jujunet37/CAM10-Astronomy-camera/Cam 10 ASCOM version/Component list/Bill_Of_Mats_Cam10R.png

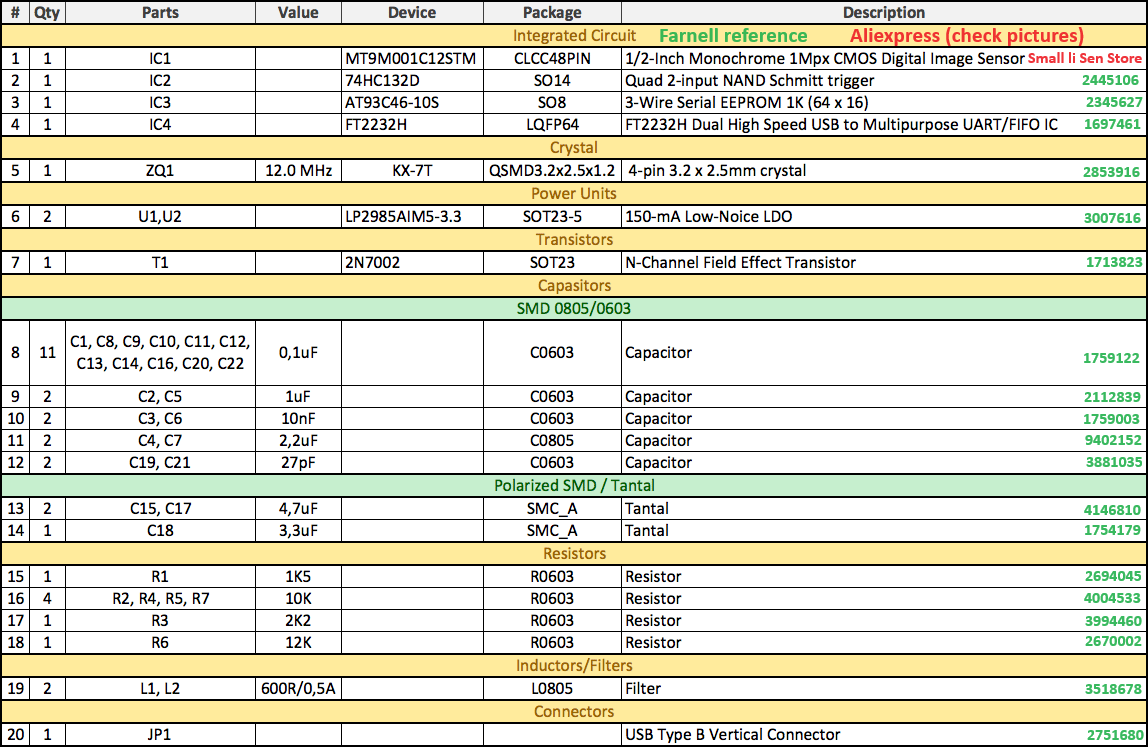
Cam 10 ASCOM version/Component list/Bill_Of_Mats_Cam10R.png
