jujunet37/CAM10-Astronomy-camera/Cam 10 ASCOM version/Component list/ressorts.jpg

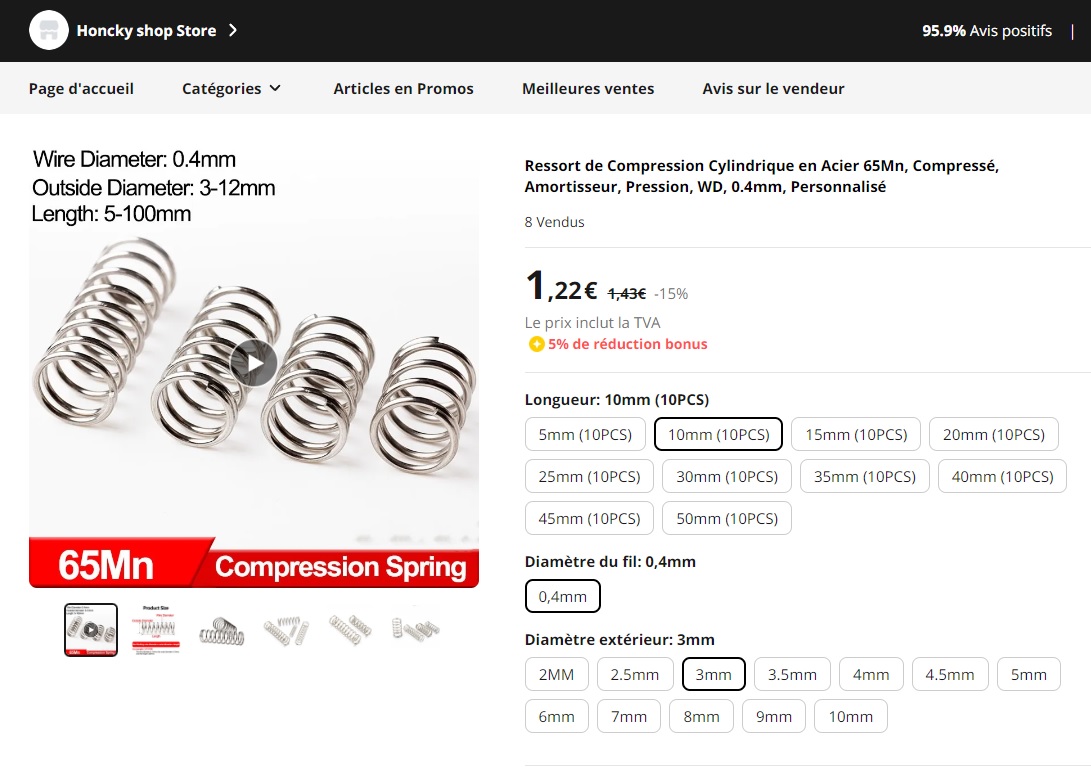
Cam 10 ASCOM version/Component list/ressorts.jpg
