jujunet37/CAM10-Astronomy-camera/Cam 10 ASCOM version/Component list/Sensor.jpg

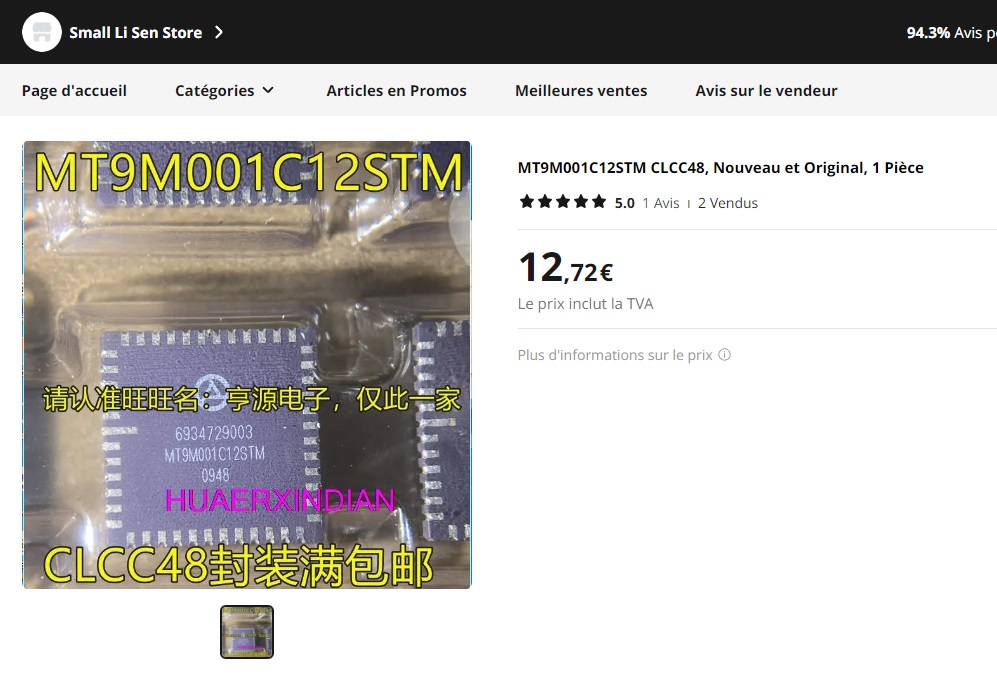
Cam 10 ASCOM version/Component list/Sensor.jpg
