jujunet37/CAM10-Astronomy-camera/Cam 10 ASCOM version/Component list/T2_Ring_ASCOM.jpg

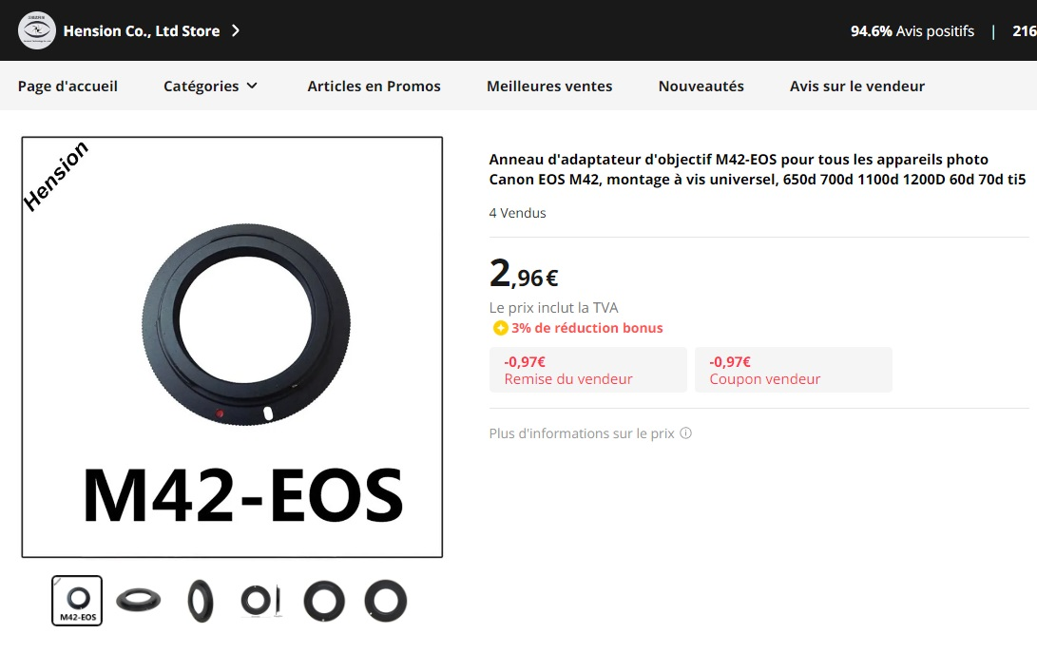
Cam 10 ASCOM version/Component list/T2_Ring_ASCOM.jpg
