jujunet37/CAM10-Astronomy-camera/Cam 10 ASCOM version/Component list/USB_Cable.jpg

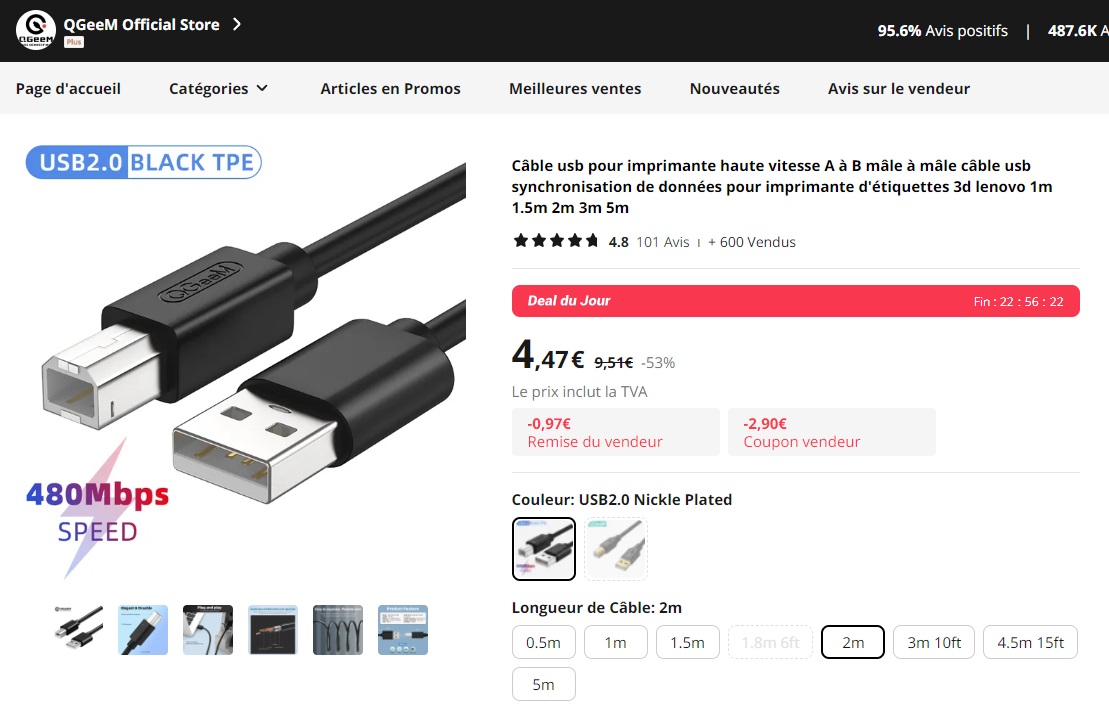
Cam 10 ASCOM version/Component list/USB_Cable.jpg
