jujunet37/CAM10-Astronomy-camera/Cam 10 Com version/Components list/Heatsink_COM.jpg

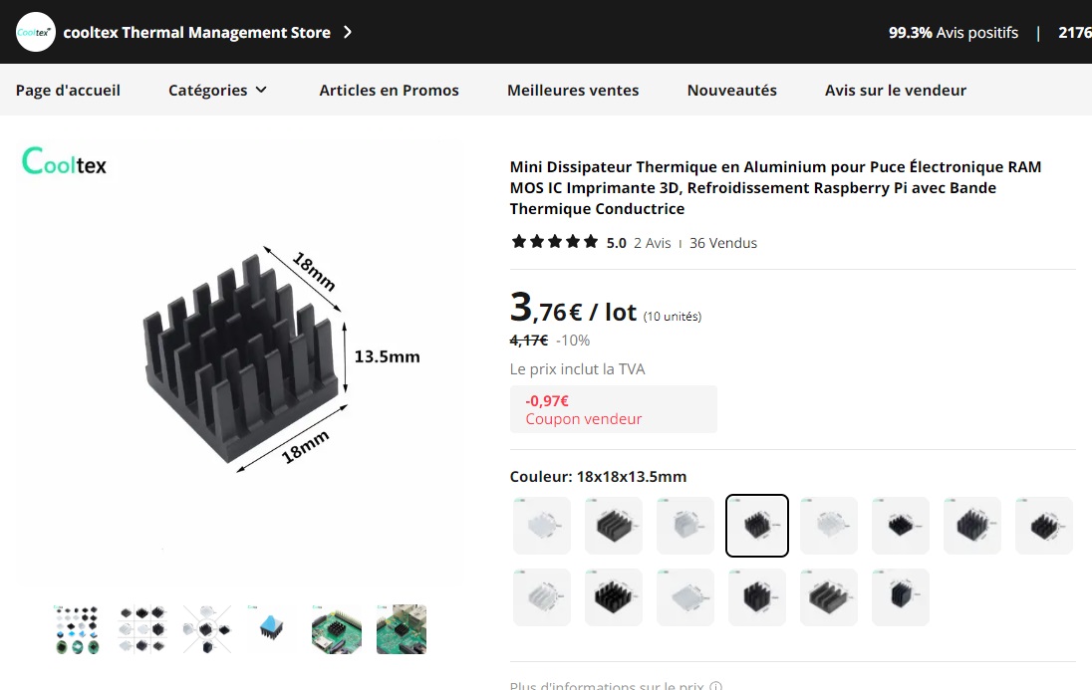
Cam 10 Com version/Components list/Heatsink_COM.jpg
