jujunet37/CAM10-Astronomy-camera/Cam 10 Com version/Components list/JST_connectors.jpg

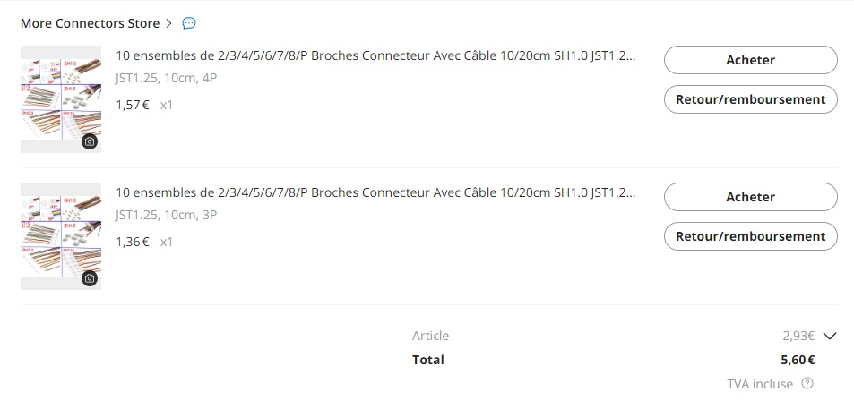
Cam 10 Com version/Components list/JST_connectors.jpg
