jujunet37/CAM10-Astronomy-camera/Cam 10 Com version/Components list/STLINK.jpg

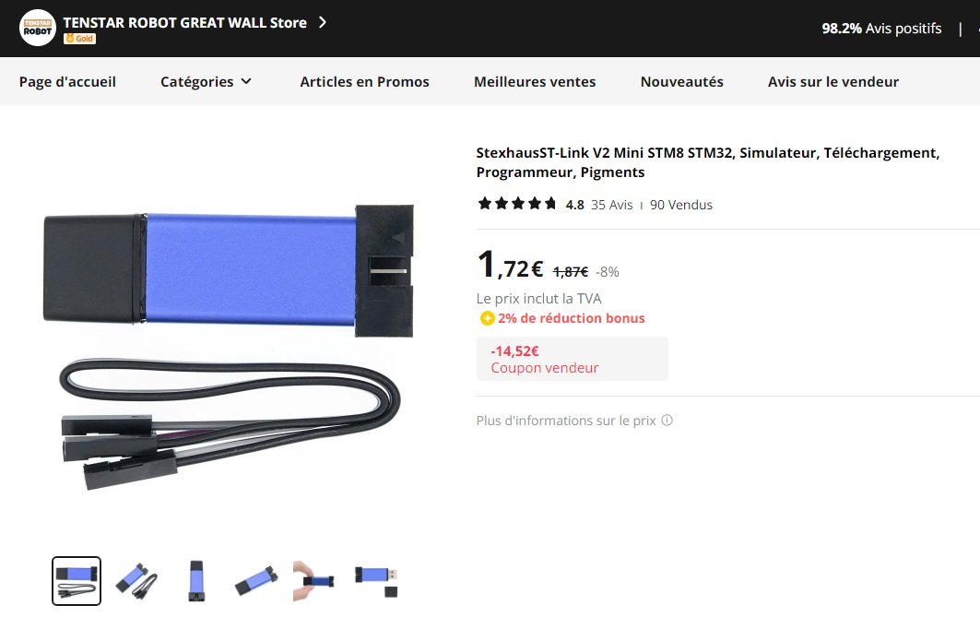
Cam 10 Com version/Components list/STLINK.jpg
