jujunet37/CAM10-Astronomy-camera/Cam 10 Com version/Components list/T2_Ring.jpg

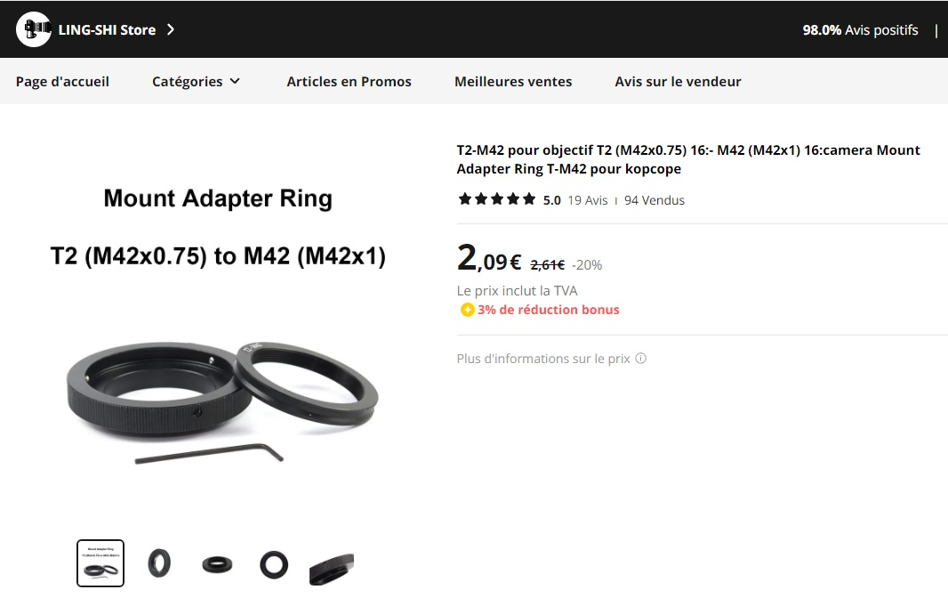
Cam 10 Com version/Components list/T2_Ring.jpg
