jujunet37/CAM10-Astronomy-camera/Cam 10 Com version/Components list/USB3300_EZK.jpg

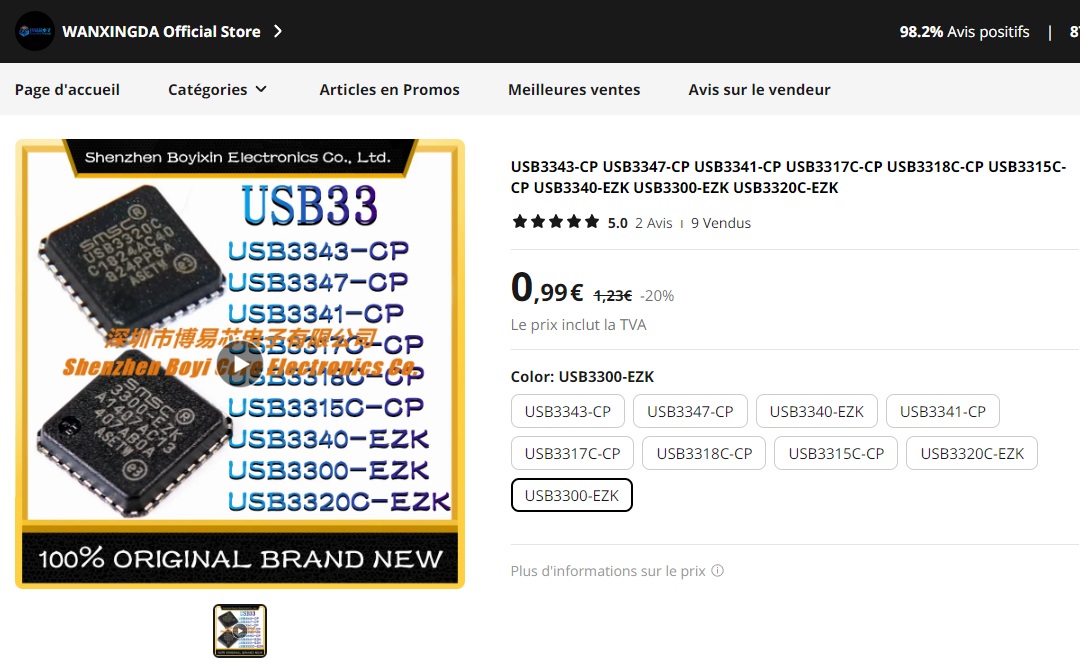
Cam 10 Com version/Components list/USB3300_EZK.jpg
