jujunet37/CAM10-Astronomy-camera/Cam 10 ASCOM version/Component list/Other Stuff/HotAir_Solder.jpg

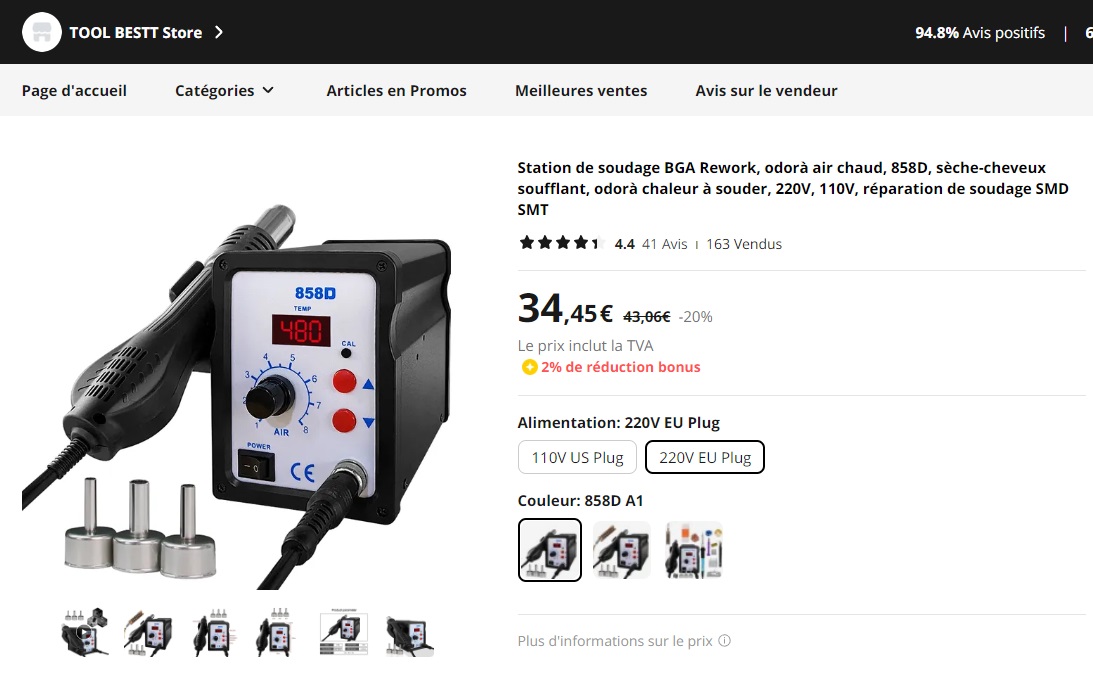
Cam 10 ASCOM version/Component list/Other Stuff/HotAir_Solder.jpg
