jujunet37/CAM10-Astronomy-camera/Cam 10 ASCOM version/Component list/Other Stuff/Tester.jpg

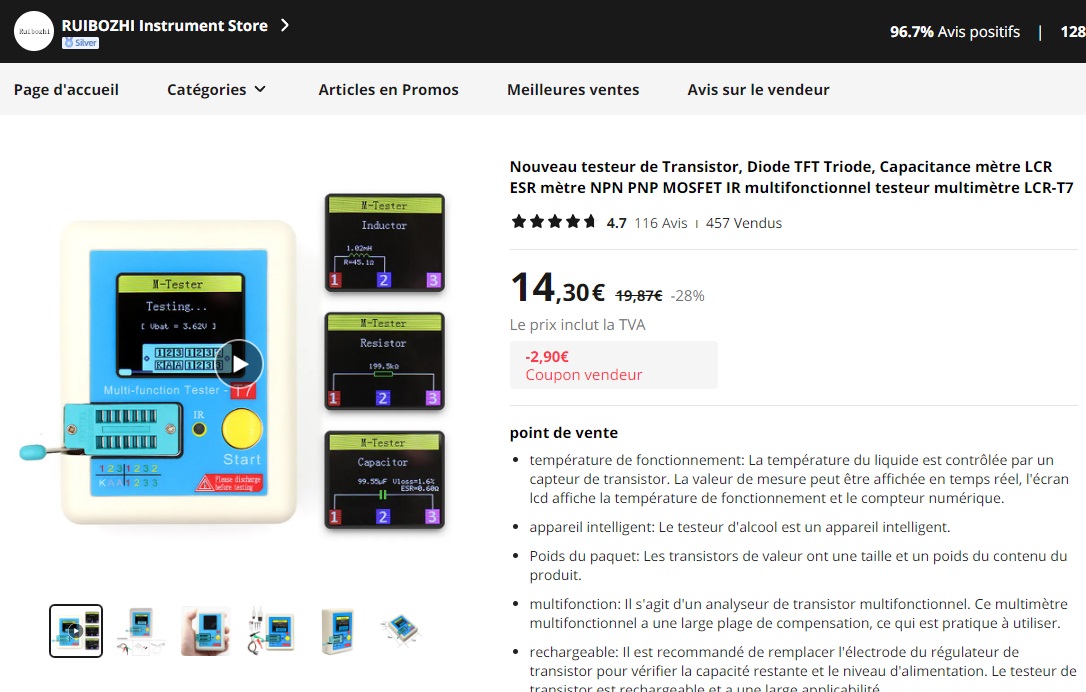
Cam 10 ASCOM version/Component list/Other Stuff/Tester.jpg
